KardosMilan/EMC_Design_Rules_Validation/01_Documents/Filter_design/2024-07-24_12h24_09.png

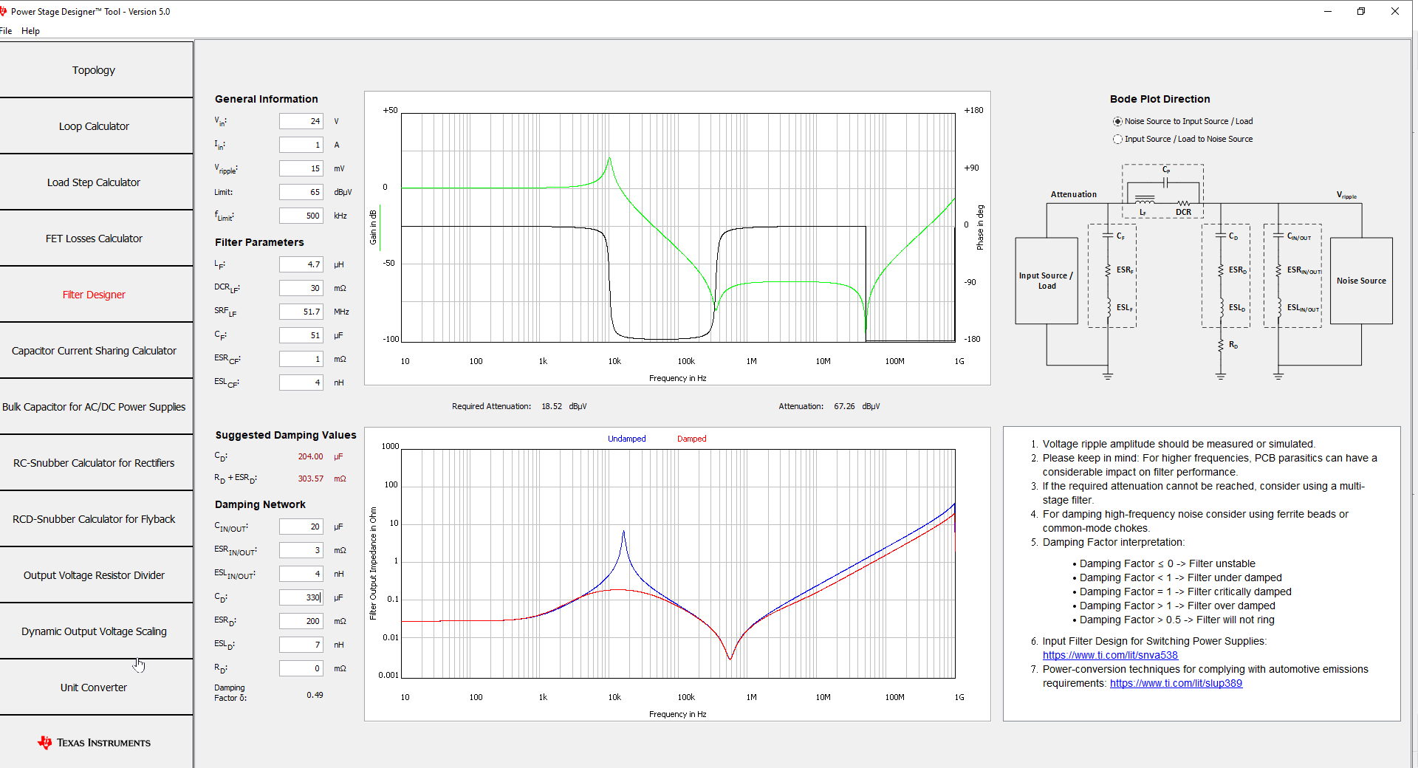
01_Documents/Filter_design/2024-07-24_12h24_09.png
