KardosMilan/EMC_Design_Rules_Validation/01_Documents/Filter_design/Final_Filter2.png

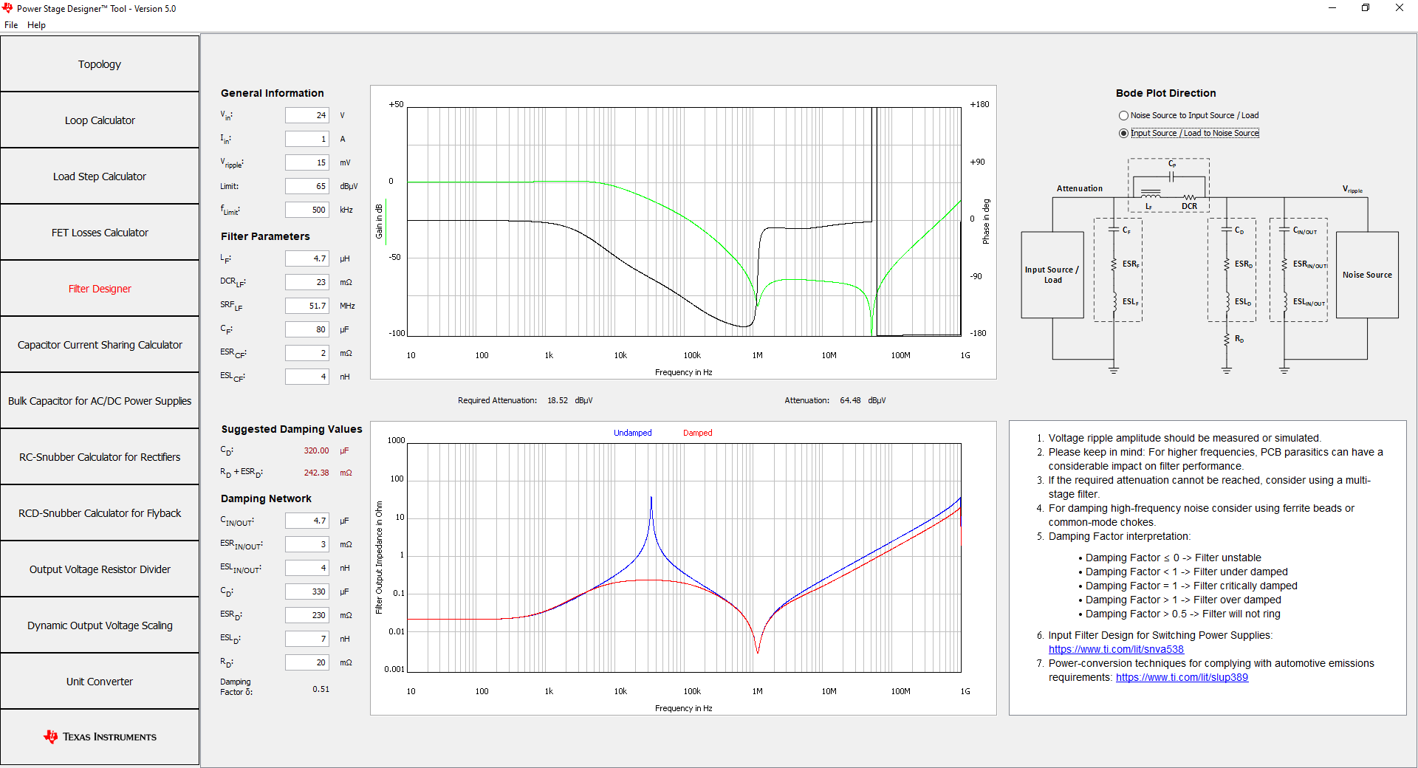
01_Documents/Filter_design/Final_Filter2.png
