KardosMilan/EMC_Design_Rules_Validation/02_Pictures/50Ohm_Loadbox_2.jpg

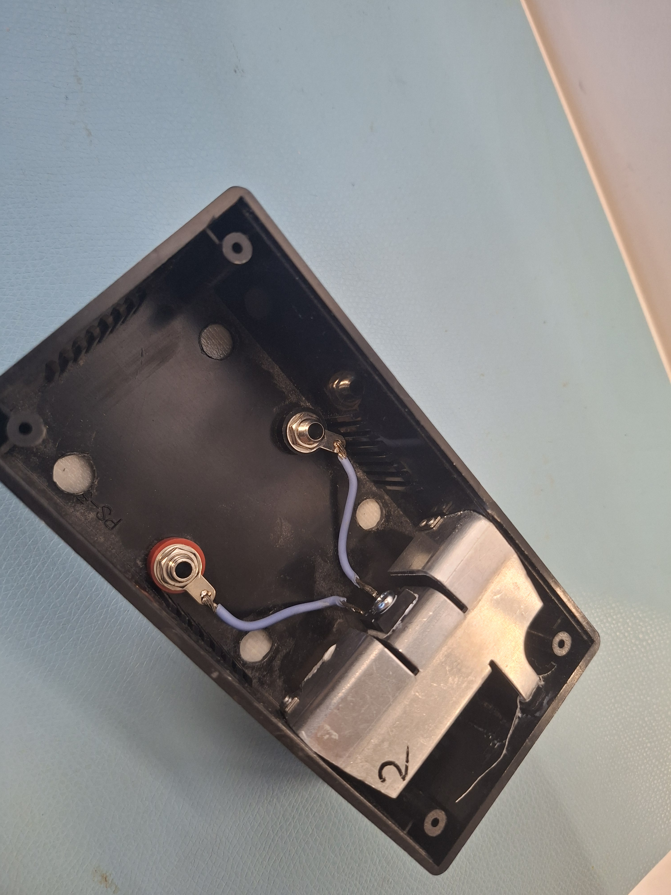
02_Pictures/50Ohm_Loadbox_2.jpg
