KardosMilan/EMC_Design_Rules_Validation/02_Pictures/Enclosure.jpg

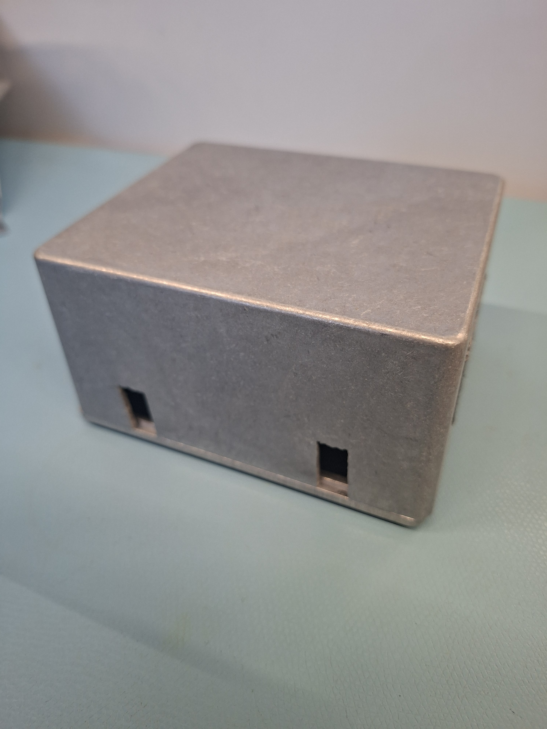
02_Pictures/Enclosure.jpg
