KardosMilan/EMC_Design_Rules_Validation/02_Pictures/Enclosure_with_PCB_2.jpg

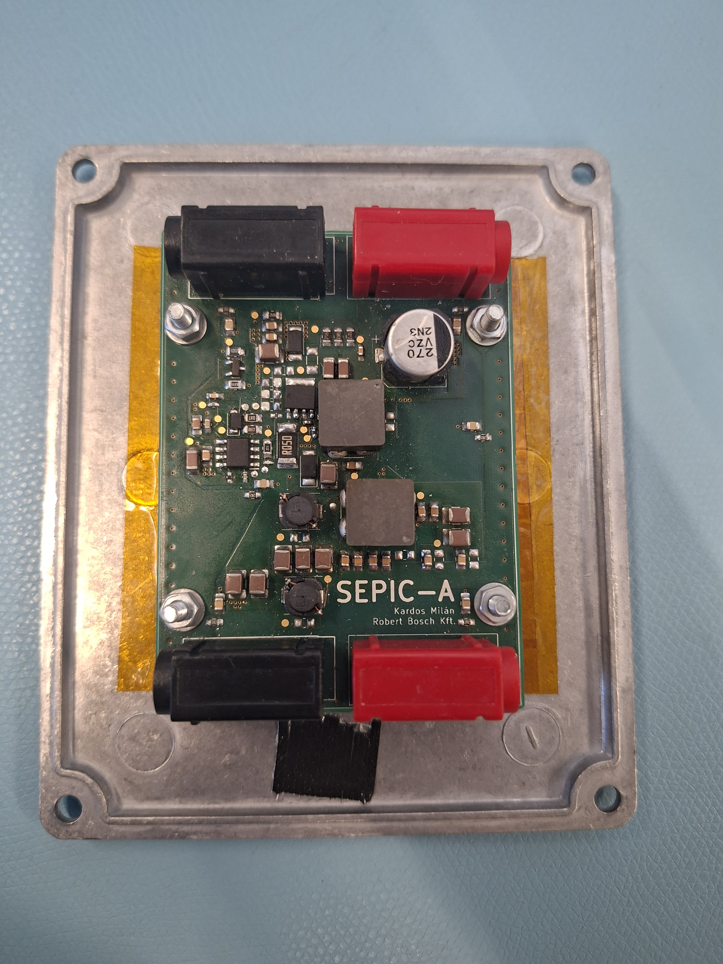
02_Pictures/Enclosure_with_PCB_2.jpg
