KardosMilan/EMC_Design_Rules_Validation/02_Pictures/SEPIC-A_bottom_view.jpg

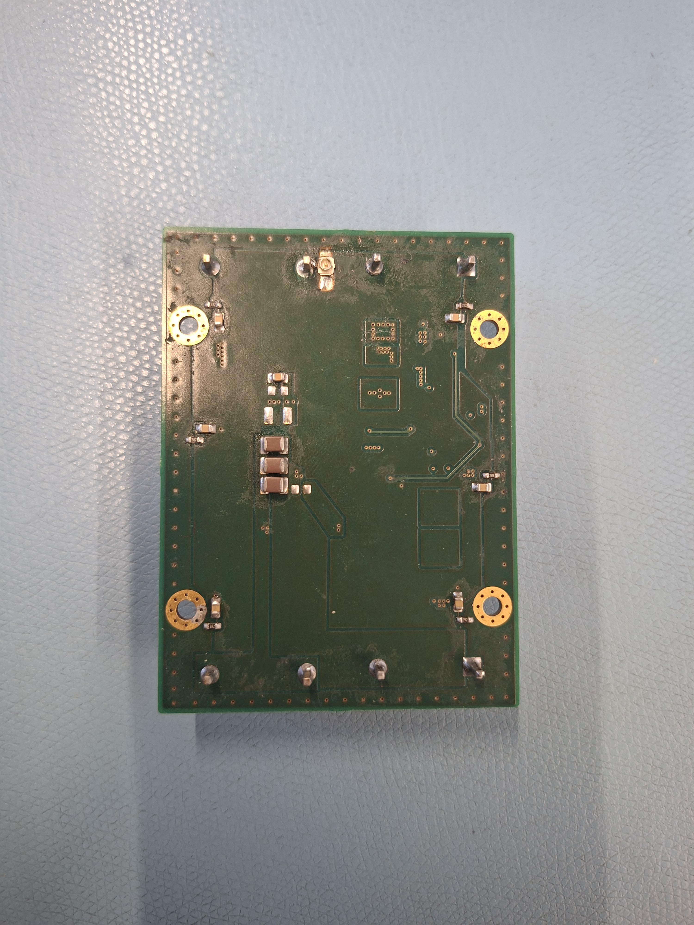
02_Pictures/SEPIC-A_bottom_view.jpg
