KardosMilan/EMC_Design_Rules_Validation/05_HW_design/SEPIC-B/MYLIB/LIB_MCAS648075-150U/MCAS648075-150U/3D/MCAS648075-150U.stp

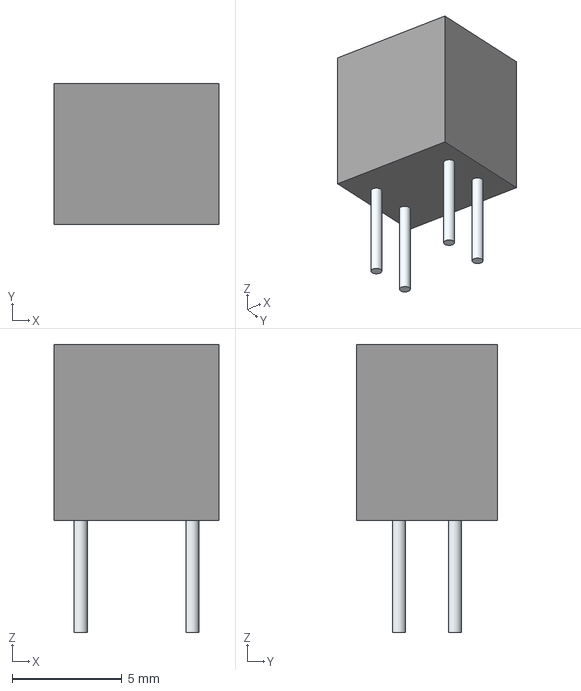
[picture p19: CAD file, 2026-06-19]
05_HW_design/SEPIC-B/MYLIB/LIB_MCAS648075-150U/MCAS648075-150U/3D/MCAS648075-150U.stp
7.50 x 6.40 x 13.1 mm
Leads
