KardosMilan/EMC_Design_Rules_Validation/05_HW_design/SEPIC-B/MYLIB/LIB_PLT10HH1026R0PNL/PLT10HH1026R0PNL/3D/PLT10HH1026R0PNL.stp

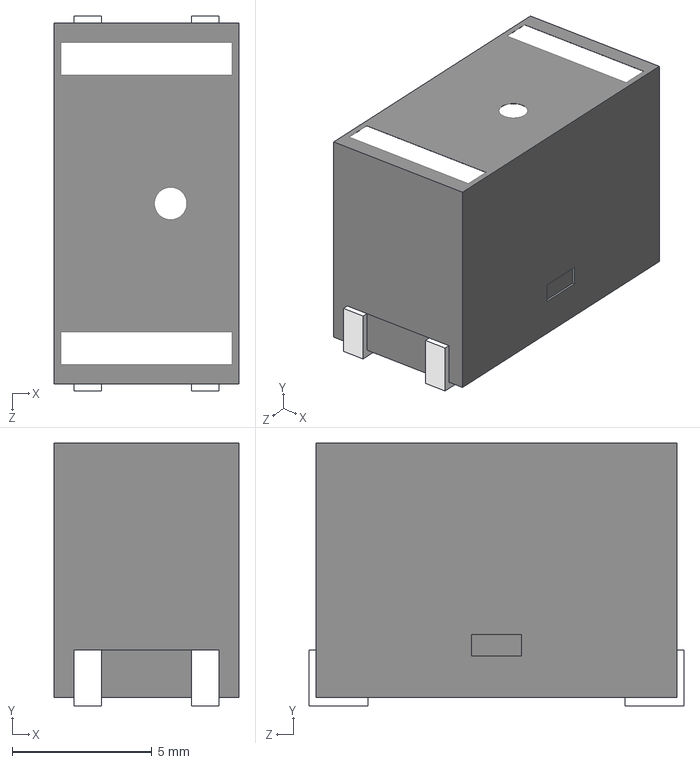
[picture p20: CAD file, 2026-06-19]
05_HW_design/SEPIC-B/MYLIB/LIB_PLT10HH1026R0PNL/PLT10HH1026R0PNL/3D/PLT10HH1026R0PNL.stp
6.60 x 9.40 x 13.4 mm
