KardosMilan/EMC_Design_Rules_Validation/05_HW_design/SEPIC-B/MYLIB/LIB_PLT10HH9016R0PNL/PLT10HH9016R0PNL/3D/PLT10HH9016R0PNL.stp

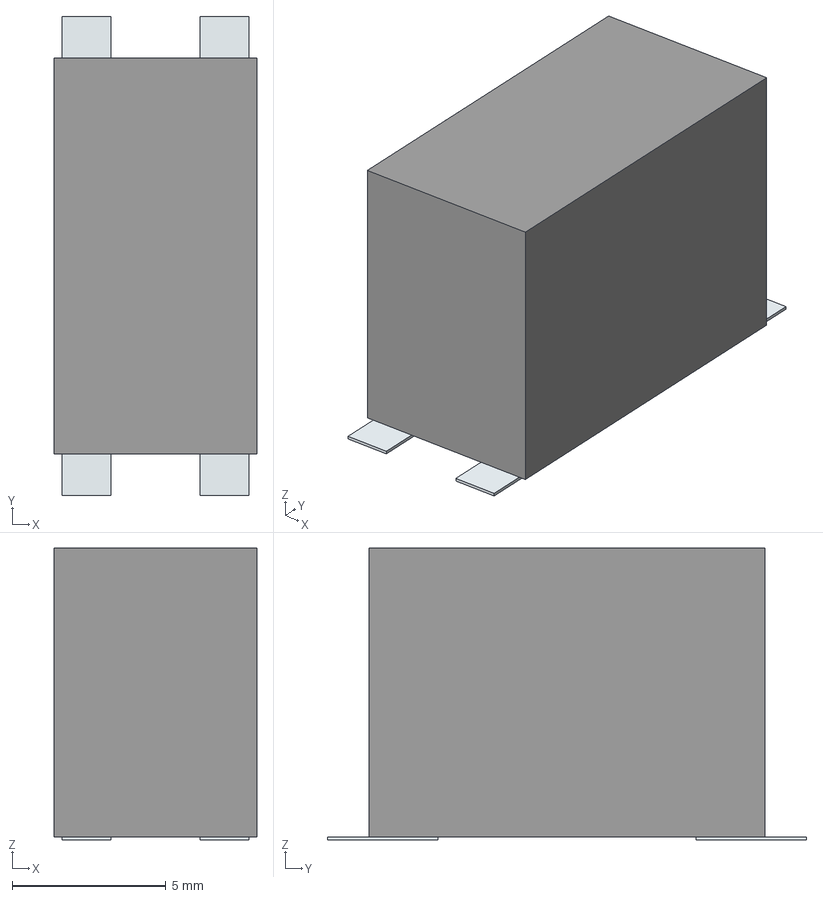
[picture p21: CAD file, 2026-06-19]
05_HW_design/SEPIC-B/MYLIB/LIB_PLT10HH9016R0PNL/PLT10HH9016R0PNL/3D/PLT10HH9016R0PNL.stp
6.60 x 15.6 x 9.50 mm
Pins
