KardosMilan/EMC_Design_Rules_Validation/05_HW_design/SEPIC-B/MYLIB/LIB_SU10VD-20010/SU10VD-20010/3D/SU10VD-20010.stp

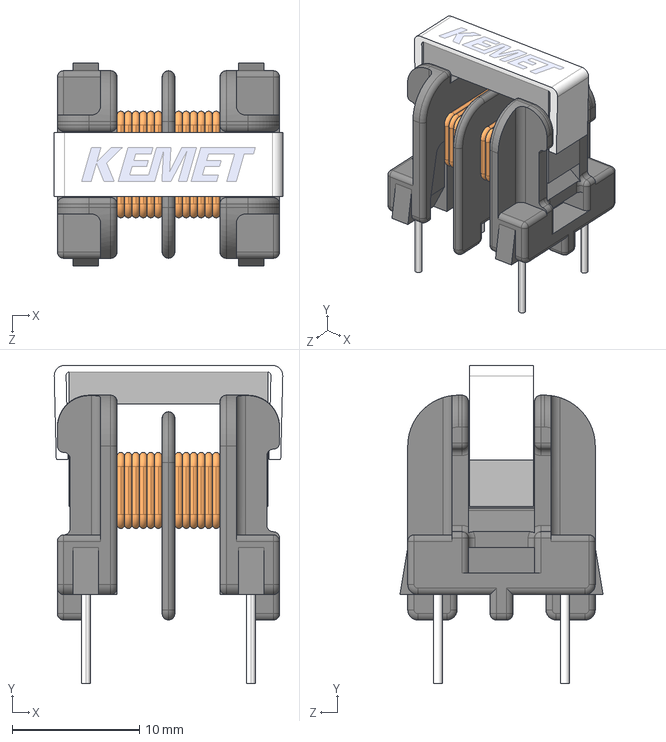
[picture p22: CAD file, 2026-06-19]
05_HW_design/SEPIC-B/MYLIB/LIB_SU10VD-20010/SU10VD-20010/3D/SU10VD-20010.stp
18.0 x 25.0 x 16.0 mm
