KardosMilan/EMC_Design_Rules_Validation/01_Documents/MEASUREMENTS/CEV_measurement_setup/20241011_093656.jpg

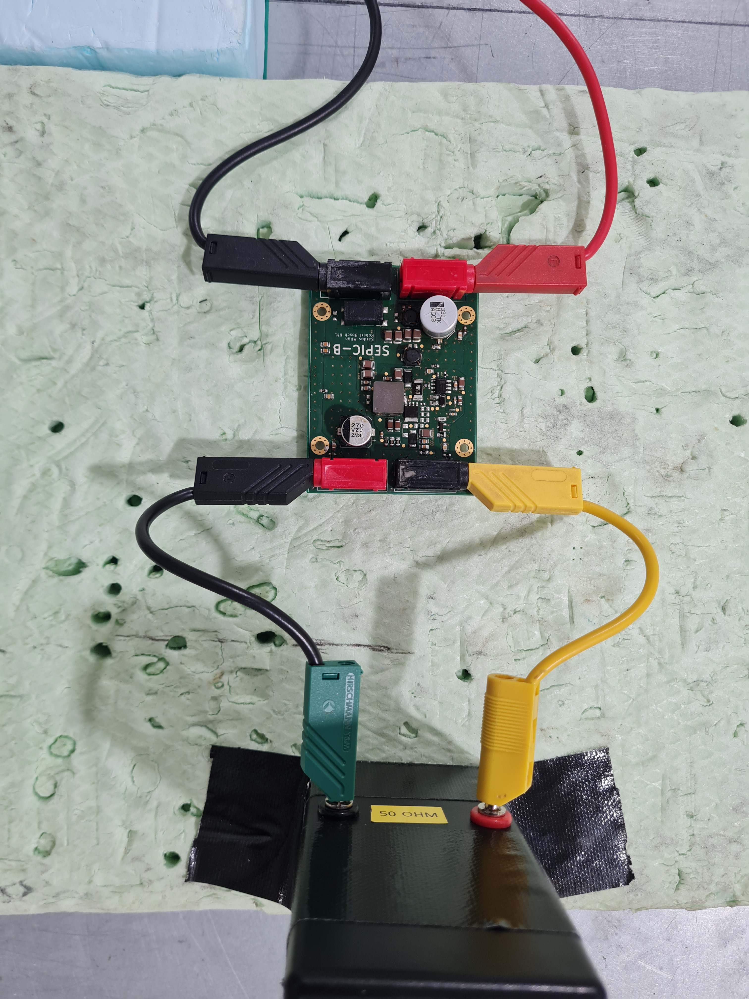
01_Documents/MEASUREMENTS/CEV_measurement_setup/20241011_093656.jpg
