KardosMilan/EMC_Design_Rules_Validation/01_Documents/MEASUREMENTS/REA_measurement_setup/IMG_0638.JPG

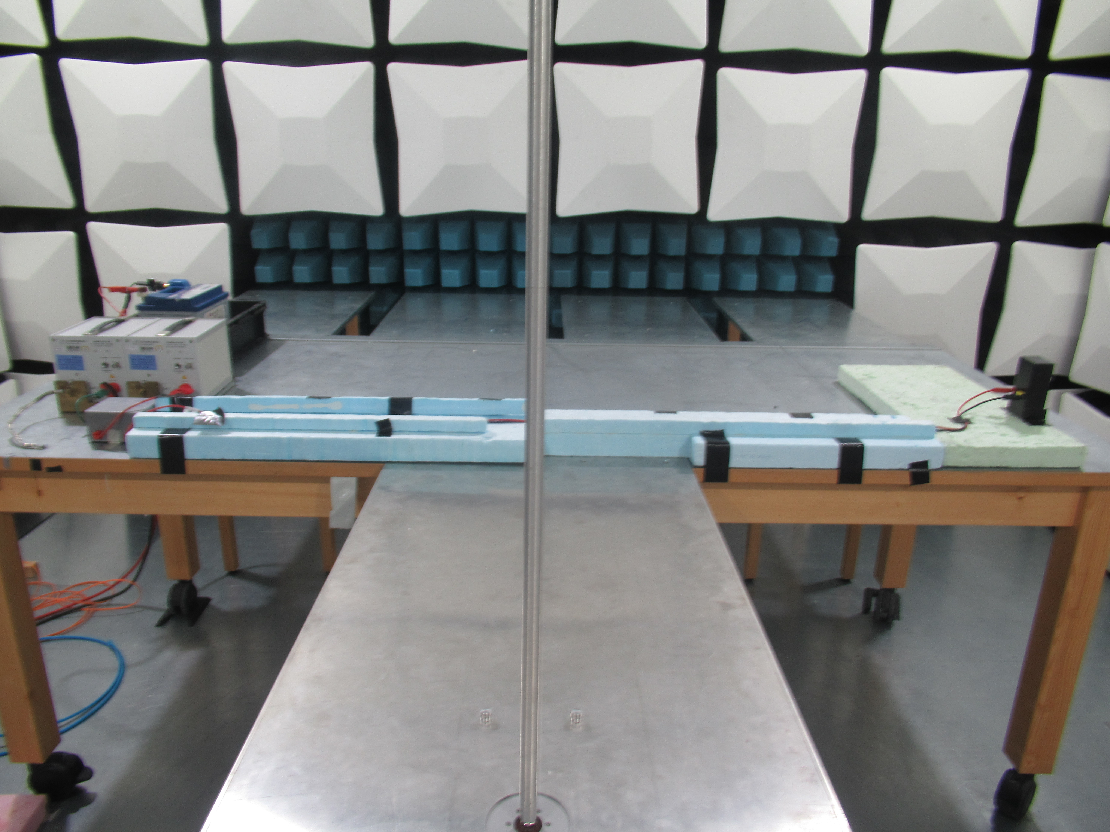
01_Documents/MEASUREMENTS/REA_measurement_setup/IMG_0638.JPG
