KardosMilan/EMC_Design_Rules_Validation/01_Documents/MEASUREMENTS/FLIR_Thermal_Camera_Pictures/FLIR0266.jpg

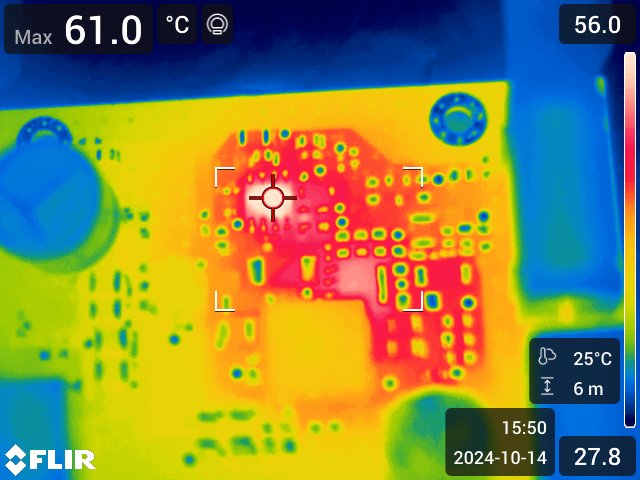
01_Documents/MEASUREMENTS/FLIR_Thermal_Camera_Pictures/FLIR0266.jpg
