KardosMilan/EMC_Design_Rules_Validation/01_Documents/MEASUREMENTS/Oscilloscope_Screenshots/310mhz_150ma.png

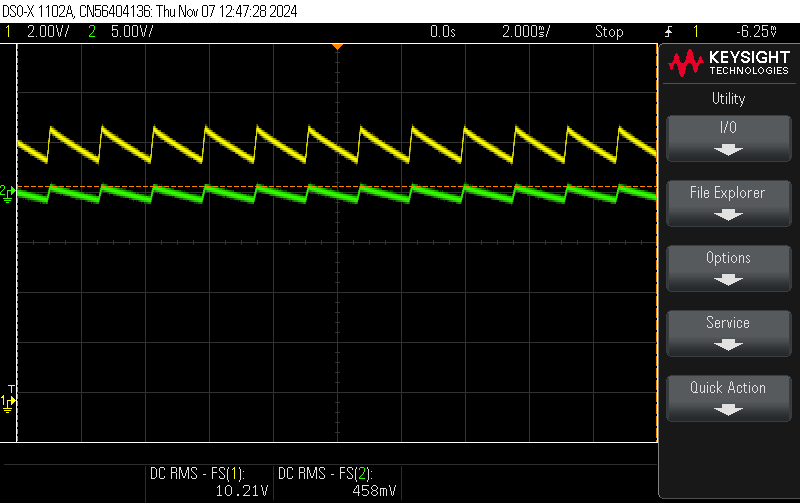
01_Documents/MEASUREMENTS/Oscilloscope_Screenshots/310mhz_150ma.png
