KardosMilan/EMC_Design_Rules_Validation/01_Documents/MEASUREMENTS/Oscilloscope_Screenshots/327mhz_150ma1.png

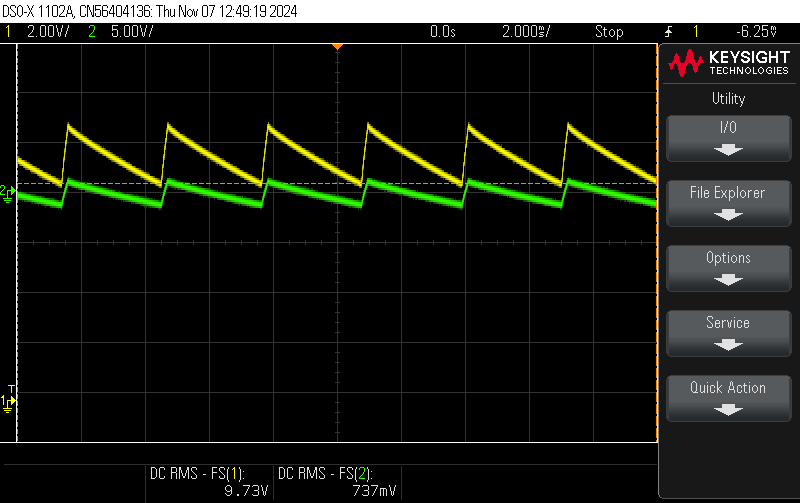
01_Documents/MEASUREMENTS/Oscilloscope_Screenshots/327mhz_150ma1.png
