KardosMilan/EMC_Design_Rules_Validation/01_Documents/MEASUREMENTS/Oscilloscope_Screenshots/377mhz_150ma3.png

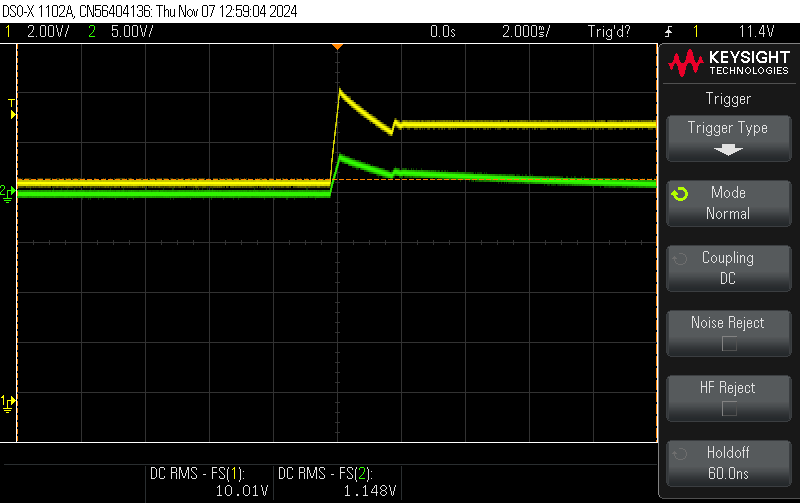
01_Documents/MEASUREMENTS/Oscilloscope_Screenshots/377mhz_150ma3.png
