KardosMilan/EMC_Design_Rules_Validation/01_Documents/MEASUREMENTS/Oscilloscope_Screenshots/scope_24.png

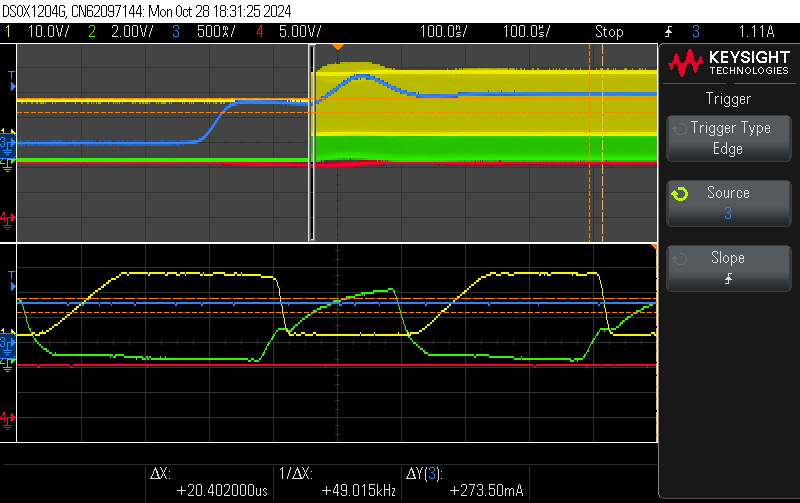
01_Documents/MEASUREMENTS/Oscilloscope_Screenshots/scope_24.png
