KardosMilan/EMC_Design_Rules_Validation/01_Documents/MEASUREMENTS/Oscilloscope_Screenshots/scope_28.png

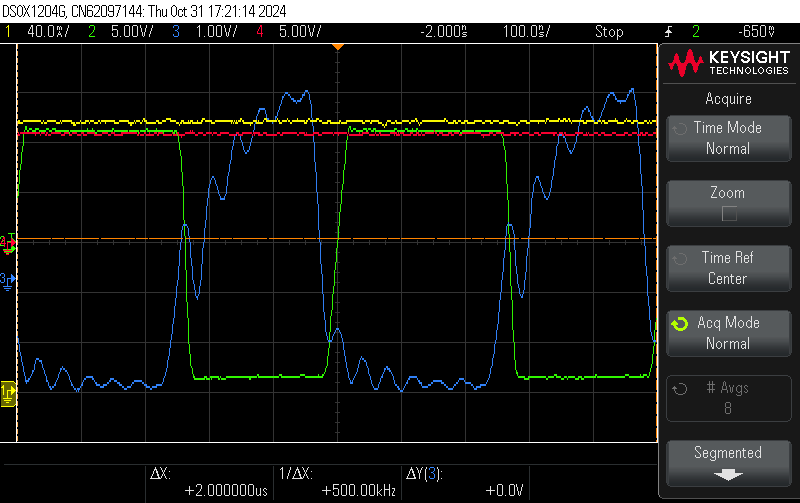
01_Documents/MEASUREMENTS/Oscilloscope_Screenshots/scope_28.png
