KardosMilan/EMC_Design_Rules_Validation/02_Pictures/SEPIC-B_top_view.jpg

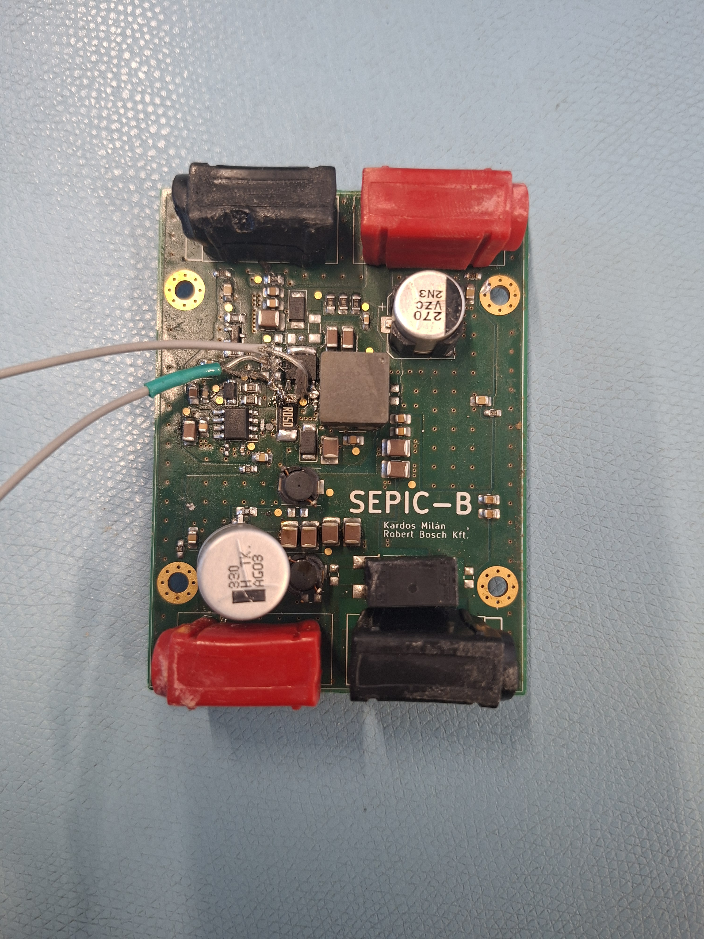
02_Pictures/SEPIC-B_top_view.jpg
